dymczykm/sony_kss_laser_driver/pictures/IMG_1101.JPG

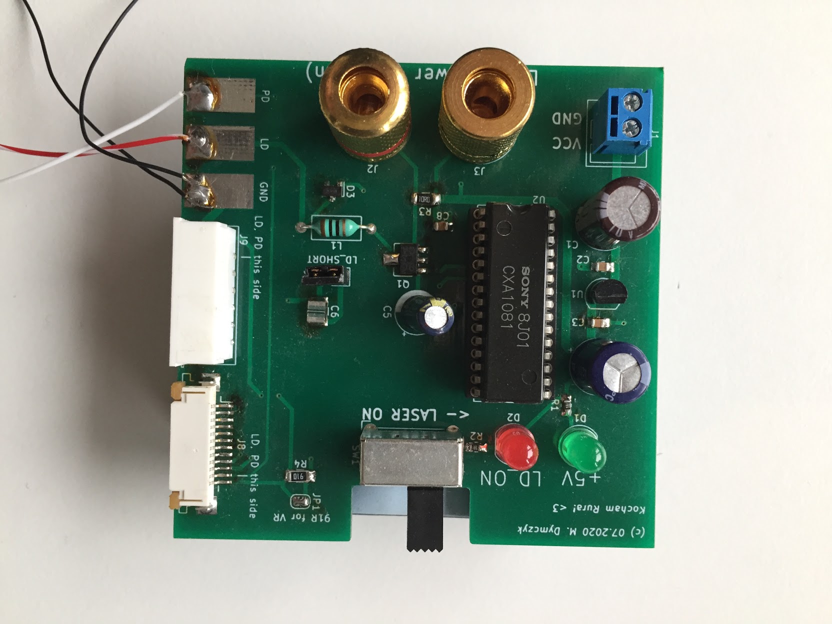
pictures/IMG_1101.JPG
